nicholasshort/GuitarFX/GuitarFX-Firmware/DriversBoard/Inc/PCM3060-Codec.h

/*
 * PCM3060-Codec.h
 *
 *  Created on: Oct 31, 2024
 *      Author: Nicholas Short
 */

#ifndef INC_PCM3060_CODEC_H_
#define INC_PCM3060_CODEC_H_

#include "main.h"
#include <stdint.h>

// Functions
uint8_t PCM3060_Init();
void	PCM3060_Reset();

#endif /* INC_PCM3060_CODEC_H_ */
